rtyle/artlight/project/eagle/projects/ray/ray0.png

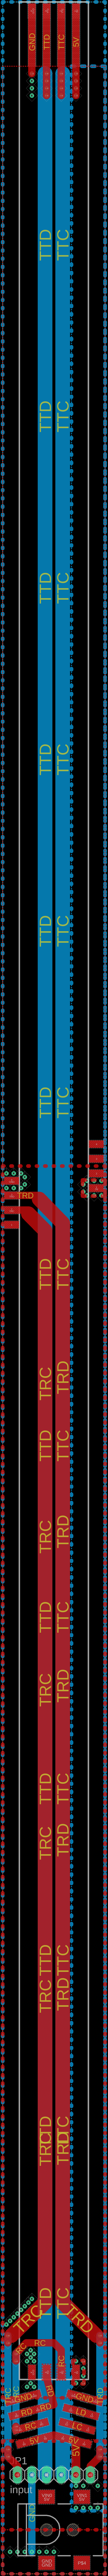
project/eagle/projects/ray/ray0.png
