rtyle/artlight/project/main/HT7M2xxxMotionSensor.cpp

#include <cinttypes>

#include "esp_log.h"

#include "HT7M2xxxMotionSensor.h"

// symmetric encode/decode for 16 bit value
// between BYTE_ORDER of our processor
// and BIG_ENDIAN encoding of device registers
static uint16_t translate(uint16_t value) {
    return
#if BYTE_ORDER == BIG_ENDIAN
    value;
#else
    __builtin_bswap16(value);
#endif
}

// scope of everything in this anonymous namespace
// is limited to this translation unit and has internal linkage
namespace {

struct RegisterKey {
    enum : uint8_t {
	configuration0			= 0x00,
	configuration1			= 0x01,
	configuration2			= 0x02,
	triggerDuration			= 0x03,
	eepromAccess			= 0x04,
	pirRawData			= 0x05,
	opticalSensorRawData		= 0x06,
	temperatureSensorRawData	= 0x07,
	status				= 0x08,
	manufacturerId			= 0x09,
	firmwareVersion			= 0x0a,
    };
};

}

HT7M2xxxMotionSensor::HT7M2xxxMotionSensor(
    asio::io_context &	io_,
    I2C::Master const *	i2cMaster_)
:
    MotionSensor	{"HT7M2xxx", io_},
    i2cMaster		{i2cMaster_}
{
    assertId();
    timer.start();
}

// how long we should wait for commands to complete
static TickType_t constexpr wait {1};

uint16_t HT7M2xxxMotionSensor::getRegister(uint8_t key) const {
    uint16_t value;
    i2cMaster->commands(address, wait)
	.writeByte(key)
	.startRead()
	.readBytes(&value, sizeof value);
    return value;
}

void HT7M2xxxMotionSensor::setRegister(uint8_t key, uint16_t value) const {
    i2cMaster->commands(address, wait)
	.writeByte(key)
	.writeBytes(&value, sizeof value);
}

void HT7M2xxxMotionSensor::assertId() const {
    assert(0x04d9 == getManufacturerId());
}

HT7M2xxxMotionSensor::Configuration0::Configuration0(
    uint16_t encoding_)
:
    encoding	{encoding_}
{}

HT7M2xxxMotionSensor::Configuration0::Configuration0(
    signed	temperatureCelsius_,
    unsigned	pirPeriod_)
:
    temperatureCelsius	{temperatureCelsius_},
    pirPeriod		{pirPeriod_}
{}

#define setter(name) HT7M2xxxMotionSensor::Configuration0 & HT7M2xxxMotionSensor::Configuration0::name##_(decltype(name) s) {name = s; return *this;}
setter(temperatureCelsius)
setter(pirPeriod)
#undef setter

HT7M2xxxMotionSensor::Configuration0
HT7M2xxxMotionSensor::getConfiguration0() const {
    return getRegister(RegisterKey::configuration0);
}

void HT7M2xxxMotionSensor::setConfiguration0(Configuration0 value) const {
    setRegister(RegisterKey::configuration0, value.encoding);
}

HT7M2xxxMotionSensor::Configuration1::Configuration1(
    uint16_t encoding_)
:
    encoding	{encoding_}
{}

HT7M2xxxMotionSensor::Configuration1::Configuration1(
    unsigned	lowVoltageDetectThreshold_,
    bool	lowVoltageDetectEnable_,
    bool	pirDetectEnable_,
    bool	pirRetrigger_,
    bool	pirTriggeredPinEnable_,
    unsigned	pirThreshold_,
    unsigned	pirGain_)
:
#if BYTE_ORDER == BIG_ENDIAN
    lowVoltageDetectThreshold	{lowVoltageDetectThreshold_},
    lowVoltageDetectEnable	{lowVoltageDetectEnable_},
    pirDetectEnable		{pirDetectEnable_},
    pirRetrigger		{pirRetrigger_},
    pirTriggeredPinEnable	{pirTriggeredPinEnable_},
    pirThreshold		{pirThreshold_},
    pirGain			{pirGain_}
#else
    pirTriggeredPinEnable	{pirTriggeredPinEnable_},
    pirRetrigger		{pirRetrigger_},
    pirDetectEnable		{pirDetectEnable_},
    lowVoltageDetectEnable	{lowVoltageDetectEnable_},
    lowVoltageDetectThreshold	{lowVoltageDetectThreshold_},
    pirGain			{pirGain_},
    pirThreshold		{pirThreshold_}
#endif
{}

#define setter(name) HT7M2xxxMotionSensor::Configuration1 & HT7M2xxxMotionSensor::Configuration1::name##_(decltype(name) s) \
    {name = s; return *this;}
setter(pirTriggeredPinEnable)
setter(pirRetrigger)
setter(pirDetectEnable)
setter(lowVoltageDetectEnable)
setter(lowVoltageDetectThreshold)
setter(pirGain)
setter(pirThreshold)
#undef setter

HT7M2xxxMotionSensor::Configuration1
HT7M2xxxMotionSensor::getConfiguration1() const {
    return getRegister(RegisterKey::configuration1);
}

void HT7M2xxxMotionSensor::setConfiguration1(Configuration1 value) const {
    setRegister(RegisterKey::configuration1, value.encoding);
}

HT7M2xxxMotionSensor::Configuration2::Configuration2(
    uint16_t encoding_)
:
    encoding	{encoding_}
{}

HT7M2xxxMotionSensor::Configuration2::Configuration2(
    unsigned	darkThreshold_,
    bool	pirDetectIfDarkEnable_,
    unsigned	address_)
:
#if BYTE_ORDER == BIG_ENDIAN
    darkThreshold		{darkThreshold_},
    pirDetectIfDarkEnable	{pirDetectIfDarkEnable_},
    address			{address_}
#else
    pirDetectIfDarkEnable	{pirDetectIfDarkEnable_},
    darkThreshold		{darkThreshold_},
    address			{address_}
#endif
{}

#define setter(name) HT7M2xxxMotionSensor::Configuration2 & HT7M2xxxMotionSensor::Configuration2::name##_(decltype(name) s) {name = s; return *this;}
setter(pirDetectIfDarkEnable)
setter(darkThreshold)
setter(address)
#undef setter

HT7M2xxxMotionSensor::Configuration2
HT7M2xxxMotionSensor::getConfiguration2() const {
    return getRegister(RegisterKey::configuration2);
}

void HT7M2xxxMotionSensor::setConfiguration2(Configuration2 value) const {
    setRegister(RegisterKey::configuration2, value.encoding);
}

unsigned HT7M2xxxMotionSensor::getDuration() const {
    return translate(getRegister(RegisterKey::triggerDuration));
}

void HT7M2xxxMotionSensor::setDuration(unsigned value) {
    MotionSensor::setDuration(value);
    setRegister(RegisterKey::triggerDuration, translate(value));
}

unsigned HT7M2xxxMotionSensor::getPirRawData() const {
    return translate(getRegister(RegisterKey::pirRawData));
}

unsigned HT7M2xxxMotionSensor::getOpticalSensorRawData() const {
    return translate(getRegister(RegisterKey::opticalSensorRawData));
}

unsigned HT7M2xxxMotionSensor::getTemperatureSensorRawData() const {
    return translate(getRegister(RegisterKey::temperatureSensorRawData));
}

HT7M2xxxMotionSensor::Status::Status(
    uint16_t encoding_)
:
    encoding	{encoding_}
{}

HT7M2xxxMotionSensor::Status HT7M2xxxMotionSensor::getStatus() const {
    return getRegister(RegisterKey::status);
}

unsigned HT7M2xxxMotionSensor::getManufacturerId() const {
    return translate(getRegister(RegisterKey::manufacturerId));
}

unsigned HT7M2xxxMotionSensor::getFirmwareVersion() const {
    return translate(getRegister(RegisterKey::firmwareVersion));
}

unsigned HT7M2xxxMotionSensor::getPeriod() const {
    return 50;	// * 10ms (tick) units
}

bool HT7M2xxxMotionSensor::readMotion() const {
#if 0
    {
	Configuration0 const c0 {getConfiguration0()};
	Configuration1 const c1 {getConfiguration1()};
	Configuration2 const c2 {getConfiguration2()};
	unsigned const duration {getDuration()};
	unsigned const pirRawData {getPirRawData()};
	ESP_LOGI(name, "\ttemperature %d°C\tpirPeriod %ums\tlowVoltageDetectThreshold %u\tlowVoltageDetectEnable %u\tpirDetectEnable %u\tpirRetrigger %u\tpirTriggeredPinEnable %u\tpirThreshold %.1fv\tpirGain %u\tdarkThreshold %u\tpirDetectIfDarkEnable %u\taddress %02x\tduration %ums\tpirRawData %u",
	    c0.temperatureCelsius,
	    pirPeriodDecode(c0.pirPeriod),
	    c1.lowVoltageDetectThreshold,
	    c1.lowVoltageDetectEnable,
	    c1.pirDetectEnable,
	    c1.pirRetrigger,
	    c1.pirTriggeredPinEnable,
	    pirThresholdDecode(c1.pirThreshold),
	    pirGainDecode(c1.pirGain),
	    c2.darkThreshold,
	    c2.pirDetectIfDarkEnable,
	    c2.address,
	    duration * 100,
	    pirRawData);
    }
#endif
#if 0
    for (auto i = 0u; ; ++i) {
	try {
	    getStatus();
	} catch (...) {
	    ESP_LOGE(name, "%p getStatus count %u", nullptr, i);
	    return false;
	}
    }
#endif
#if 0
    {
	Status const status {getStatus()};
	ESP_LOGI(name, "notReady %u\tlowVoltageDetected %u\tdark %u\tpirNoiseDetected %u\tpirRetriggered %u\tpirTriggered %u",
	    status.notReady,
	    status.lowVoltageDetected,
	    status.dark,
	    status.pirNoiseDetected,
	    status.pirRetriggered,
	    status.pirTriggered);
    }
#endif
    return getStatus().pirTriggered;
}

HT7M2xxxMotionSensor::~HT7M2xxxMotionSensor() {}
