rtyle/artlight/project/main/LuxSensor.cpp

#include "esp_log.h"

#include "LuxSensor.h"

LuxSensor::LuxSensor(char const * name_, asio::io_context & io_)
:
    name	{name_},
    io		{io_},
    lux		{0.0f},
    // asio timers are not supported
    // adapt a FreeRTOS timer to post an update
    timer{name,
	1,
	false,
	[this]() {
	    io.post([this]() {
		this->update();
	    });
	}
    }
{}

LuxSensor::~LuxSensor() {}

static TickType_t soonAfterAvailable(unsigned available) {
    return 2 + available / portTICK_PERIOD_MS;
}

void LuxSensor::update() {
    // we try to skate on the edge (just under an overflow_error)
    bool up {true};
    try {
	lux = readLux();
    } catch (std::underflow_error & e) {
#if 0
	ESP_LOGE(name, "underflow %s", e.what());
#endif
    } catch (std::overflow_error & e) {
#if 0
	ESP_LOGE(name, "overflow %s", e.what());
#endif
	up = false;
    } catch (esp_err_t & e) {
	ESP_LOGE(name, "readLux %s (0x%x)", esp_err_to_name(e), e);
    } catch (...) {
	ESP_LOGE(name, "readLux unknown error");
    }
    try {
	timer.setPeriod(soonAfterAvailable(up
	    ? increaseSensitivity()
	    : decreaseSensitivity()));
    } catch (esp_err_t & e) {
	ESP_LOGE(name, "set sensitivity %s (0x%x)", esp_err_to_name(e), e);
    } catch (...) {
	ESP_LOGE(name, "unknown error");
    }
    timer.start();
}

float LuxSensor::getLux() {return lux;}
