rtyle/artlight/project/main/GoldenArtTask.cpp

#include <array>
#include <cassert>
#include <cmath>
#include <limits>
#include <random>
#include <set>
#include <sstream>
#include <vector>

#include "esp_log.h"
extern "C" {
#include "esp_time_impl.h"
}

#include "fromString.h"
#include "Array.h"
#include "Blend.h"
#include "Contrast.h"
#include "GoldenArtTask.h"
#include "Curve.h"
#include "PerlinNoise.hpp"
#include "Timer.h"
#include "TSL2591LuxSensor.h"

constexpr float pi	{std::acos(-1.0f)};
constexpr float tau	{2.0f * pi};

// https://en.wikipedia.org/wiki/Fibonacci_number
// 0, 1, 2, 3, 4, 5, 6,  7,  8,  9, 10, 11,  12, ...
// 0, 1, 1, 2, 3, 5, 8, 13, 21, 34, 55, 89, 144, ...
static constexpr unsigned fibonacci_(unsigned a, unsigned b, unsigned i) {
    return i ? fibonacci_(b, a + b, i - 1) : a + b;
}
constexpr unsigned n0 {0};
constexpr unsigned n1 {1};
static constexpr unsigned fibonacci(unsigned i) {
    return i > 1 ? fibonacci_(n0, n1, i - 2) : i ? n1 : n0;
}

constexpr unsigned millisecondsPerSecond	{1000u};
constexpr unsigned microsecondsPerSecond	{1000000u};

#define rimEnd 1024
constexpr size_t ledCount {rimEnd};

char const * const GoldenArtTask::Mode::string[]
    {"clock", "swirl", "solid"};
GoldenArtTask::Mode::Mode(Value value_) : value(value_) {}
GoldenArtTask::Mode::Mode(char const * value) : value(
    [value](){
	size_t i {0};
	for (auto e: string) {
	    if (0 == std::strcmp(e, value)) return static_cast<Value>(i);
	    ++i;
	}
	return clock;
    }()
) {}
char const * GoldenArtTask::Mode::toString() const {
    return string[value];
}

namespace {
// A Path may be used to construct a standard input iterator
// that begins at an unsigned value,
// decrements a unsigned step (default 1) as it is advanced
// until it exhausts all unsigned values on this path.
class Path {
public:
    class Iterator: public std::iterator<std::input_iterator_tag, unsigned,
	unsigned, unsigned const *, unsigned> {
    public:
	explicit Iterator(Path const * path_)
	    : path{path_}, value{path->value} {}
	explicit Iterator()
	    : path{nullptr}, value{std::numeric_limits<value_type>::max()} {}
	Iterator & operator++() {
	    if (path) {
		if (value < path->step)
		    value = std::numeric_limits<value_type>::max();
		else
		    value -= path->step;
	    }
	    return *this;
	}
	bool operator==(Iterator that) const {return value == that.value;}
	bool operator!=(Iterator that) const {return !(*this == that);}
	reference operator*() const {return value;}
    private:
	Path const * path;
	value_type value;
    };
    Path(Iterator::value_type value_, Iterator::value_type step_ = 1) : value{value_}, step{step_} {}
    Iterator begin() {return Iterator(this);}
    Iterator end() {return Iterator();}
private:
    Iterator::value_type const value;
    Iterator::value_type const step;
};
}

static constexpr float phaseIn(uint64_t time, uint64_t period) {
    return (time % period) / static_cast<float>(period);
}

static float fade_(float high, float dim, float min, float from) {
    if (1.0f <= from || 0.0f == dim || min > high) {
	return high;		// snap high
    } else {
	if (0.0f == from && 1.0 == dim) {
	    return 0.0f;	// snap off
	} else {
	    auto const low {std::max(min, high * (1.0f - dim))};
	    return low + (high - low) * from;
	}
    }
}

void GoldenArtTask::update_() {
    // LED i [0, ledCount) is rendered like a seed in a sunflower head
    // at polar coordinate
    //	(scale * sqrt(1 + i), i * tau / phi)
    // where scale was chosen to space the LEDs adequately
    // (18 mil for SK9822 5050 (5.0 x 5.0 mm) LEDs).
    //
    // such rendering creates a family of spirals for each fibonacci number N
    // where
    // * N is the number of spirals in the family and
    // * N separates neighboring LEDs in any spiral.

    // for rendering a family of spirals,
    // it is convenient to have the outermost rim of indeces (from the end)
    // of each ordered in a clockwise manner from the top.
    // these were imported from exploratory rendering code.
    // see easyeda/projects/golden/golden.html.

    #define rimName_(end, index) rim##end##_##index
    #define rimName(end, index) rimName_(end, index)
    #define rimDecl(end, index) rimName_(end, index)[fibonacci(index)]

    struct Rim {
	unsigned const	end;
	unsigned const	fibonacciIndex;
	uint8_t const *	sequence;
    };
    #define RimArgs(end, index) {end, index, rimName(end, index)}

    static constexpr uint8_t rimDecl(rimEnd, 7) {
	0,  5, 10,  2,  7, 12,  4,  9,  1,  6, 11,  3,  8,
    };
    static constexpr uint8_t rimDecl(917, 7) {
	 3,  8,  0,  5, 10,  2,  7, 12,  4,  9,  1,  6, 11,
    };
    static constexpr uint8_t rimDecl(569, 7) {
	11,  3,  8,  0,  5, 10,  2,  7, 12,  4,  9,  1,  6,
    };
    static constexpr uint8_t rimDecl(355, 7) {
	 9,  1,  6, 11,  3,  8,  0,  5, 10,  2,  7, 12,  4,
    };
    static constexpr uint8_t rimDecl(233, 7) {
	 5, 10,  2,  7, 12,  4,  9,  1,  6, 11,  3,  8,  0,
    };
    static constexpr uint8_t rimDecl(145, 7) {
	 6, 11,  3,  8,  0,  5, 10,  2,  7, 12,  4,  9,  1,
    };
    static constexpr uint8_t rimDecl( 91, 7) {
	12,  4,  9,  1,  6, 11,  3,  8,  0,  5, 10,  2,  7,
    };
    static constexpr uint8_t rimDecl( 57, 7) {
	 7, 12,  4,  9,  1,  6, 11,  3,  8,  0,  5, 10,  2,
    };
    static constexpr Rim const rim7[] {
	RimArgs(rimEnd, 7),
	RimArgs(917, 7),
	RimArgs(569, 7),
	RimArgs(355, 7),
	RimArgs(233, 7),
	RimArgs(145, 7),
	RimArgs( 91, 7),
	RimArgs( 57, 7),
    };

    static constexpr uint8_t rimDecl(rimEnd, 8) {
	 0, 13,  5, 18, 10,  2, 15,  7, 20, 12,  4, 17,  9,  1, 14,  6,
	19, 11,  3, 16,  8,
    };
    static constexpr uint8_t rimDecl(917, 8) {
	 3, 16,  8,  0, 13,  5, 18, 10,  2, 15,  7, 20, 12,  4, 17,  9,
	 1, 14,  6, 19, 11,
    };
    static constexpr uint8_t rimDecl(582, 8) {
	 3, 16,  8,  0, 13,  5, 18, 10,  2, 15,  7, 20, 12,  4, 17,  9,
	 1, 14,  6, 19, 11,
    };
    static constexpr uint8_t rimDecl(361, 8) {
	 2, 15,  7, 20, 12,  4, 17,  9,  1, 14,  6, 19, 11,  3, 16,  8,
	 0, 13,  5, 18, 10,
    };
    static constexpr uint8_t rimDecl(225, 8) {
	10,  2, 15,  7, 20, 12,  4, 17,  9,  1, 14,  6, 19, 11,  3, 16,
	 8,  0, 13,  5, 18,
    };
    static constexpr uint8_t rimDecl(141, 8) {
	15,  7, 20, 12,  4, 17,  9,  1, 14,  6, 19, 11,  3, 16,  8,  0,
	13,  5, 18, 10,  2,
    };
    static constexpr uint8_t rimDecl( 91, 8) {
	20, 12,  4, 17,  9,  1, 14,  6, 19, 11,  3, 16,  8,  0, 13,  5,
	18, 10,  2, 15,  7,
    };
    static constexpr Rim const rim8[] {
	RimArgs(rimEnd, 8),
	RimArgs(917, 8),
	RimArgs(582, 8),
	RimArgs(361, 8),
	RimArgs(225, 8),
	RimArgs(141, 8),
	RimArgs( 91, 8),
    };

    static constexpr uint8_t rimDecl(rimEnd, 9) {
	 0, 13, 26,  5, 18, 31, 10, 23,  2, 15, 28,  7, 20, 33, 12, 25,
	 4, 17, 30,  9, 22,  1, 14, 27,  6, 19, 32, 11, 24,  3, 16, 29,
	 8, 21,
    };
    static constexpr uint8_t rimDecl(917, 9) {
	 3, 16, 29,  8, 21,  0, 13, 26,  5, 18, 31, 10, 23,  2, 15, 28,
	 7, 20, 33, 12, 25,  4, 17, 30,  9, 22,  1, 14, 27,  6, 19, 32,
	11, 24,
    };
    static constexpr uint8_t rimDecl(569, 9) {
	11, 24,  3, 16, 29,  8, 21,  0, 13, 26,  5, 18, 31, 10, 23,  2,
	15, 28,  7, 20, 33, 12, 25,  4, 17, 30,  9, 22,  1, 14, 27,  6,
	19, 32,
    };
    static constexpr uint8_t rimDecl(355, 9) {
	30,  9, 22,  1, 14, 27,  6, 19, 32, 11, 24,  3, 16, 29,  8, 21,
	 0, 13, 26,  5, 18, 31, 10, 23,  2, 15, 28,  7, 20, 33, 12, 25,
	 4, 17,
    };
    static constexpr uint8_t rimDecl(225, 9) {
	10, 23,  2, 15, 28,  7, 20, 33, 12, 25,  4, 17, 30,  9, 22,  1,
	14, 27,  6, 19, 32, 11, 24,  3, 16, 29,  8, 21,  0, 13, 26,  5,
	18, 31,
    };
    static constexpr uint8_t rimDecl(141, 9) {
	15, 28,  7, 20, 33, 12, 25,  4, 17, 30,  9, 22,  1, 14, 27,  6,
	19, 32, 11, 24,  3, 16, 29,  8, 21,  0, 13, 26,  5, 18, 31, 10,
	23, 2,
    };
    static constexpr Rim const rim9[] {
	RimArgs(rimEnd, 9),
	RimArgs(917, 9),
	RimArgs(569, 9),
	RimArgs(355, 9),
	RimArgs(225, 9),
	RimArgs(141, 9),
    };

    static constexpr uint8_t rimDecl(rimEnd, 10) {
	 0, 34, 13, 47, 26,  5, 39, 18, 52, 31, 10, 44, 23,  2, 36, 15,
	49, 28,  7, 41, 20, 54, 33, 12, 46, 25,  4, 38, 17, 51, 30,  9,
	43, 22,  1, 35, 14, 48, 27,  6, 40, 19, 53, 32, 11, 45, 24,  3,
	37, 16, 50, 29,  8, 42, 21,
    };
    static constexpr uint8_t rimDecl(907, 10) {
	27,  6, 40, 19, 53, 32, 11, 45, 24,  3, 37, 16, 50, 29,  8, 42,
	21,  0, 34, 13, 47, 26,  5, 39, 18, 52, 31, 10, 44, 23,  2, 36,
	15, 49, 28,  7, 41, 20, 54, 33, 12, 46, 25,  4, 38, 17, 51, 30,
	 9, 43, 22,  1, 35, 14, 48,
    };
    static constexpr uint8_t rimDecl(582, 10) {
	24,  3, 37, 16, 50, 29,  8, 42, 21,  0, 34, 13, 47, 26,  5, 39,
	18, 52, 31, 10, 44, 23,  2, 36, 15, 49, 28,  7, 41, 20, 54, 33,
	12, 46, 25,  4, 38, 17, 51, 30,  9, 43, 22,  1, 35, 14, 48, 27,
	 6, 40, 19, 53, 32, 11, 45,
    };
    static constexpr uint8_t rimDecl(355, 10) {
	30,  9, 43, 22,  1, 35, 14, 48, 27,  6, 40, 19, 53, 32, 11, 45,
	24,  3, 37, 16, 50, 29,  8, 42, 21,  0, 34, 13, 47, 26,  5, 39,
	18, 52, 31, 10, 44, 23,  2, 36, 15, 49, 28,  7, 41, 20, 54, 33,
	12, 46, 25,  4, 38, 17, 51,
    };
    static constexpr uint8_t rimDecl(225, 10) {
	44, 23,  2, 36, 15, 49, 28,  7, 41, 20, 54, 33, 12, 46, 25,  4,
	38, 17, 51, 30,  9, 43, 22,  1, 35, 14, 48, 27,  6, 40, 19, 53,
	32, 11, 45, 24,  3, 37, 16, 50, 29,  8, 42, 21,  0, 34, 13, 47,
	26,  5, 39, 18, 52, 31, 10,
    };
    static constexpr Rim const rim10[] {
	RimArgs(rimEnd, 10),
	RimArgs(907, 10),
	RimArgs(582, 10),
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
	42, 76, 21, 55,  0, 34, 68, 13, 47, 81, 26, 60,  5, 39, 73, 18,
	52, 86, 31, 65, 10, 44, 78, 23, 57,
    };
    static constexpr Rim const rim11[] {
	RimArgs(rimEnd, 11),
	RimArgs(907, 11),
	RimArgs(569, 11),
	RimArgs(361, 11),
    };

    static constexpr uint8_t rimDecl(rimEnd, 12) {
	  0,  89,  34, 123,  68,  13, 102,  47, 136,  81,  26, 115,  60,   5,  94,  39,
	128,  73,  18, 107,  52, 141,  86,  31, 120,  65,  10,  99,  44, 133,  78,  23,
	112,  57,   2,  91,  36, 125,  70,  15, 104,  49, 138,  83,  28, 117,  62,   7,
	 96,  41, 130,  75,  20, 109,  54, 143,  88,  33, 122,  67,  12, 101,  46, 135,
	 80,  25, 114,  59,   4,  93,  38, 127,  72,  17, 106,  51, 140,  85,  30, 119,
	 64,   9,  98,  43, 132,  77,  22, 111,  56,   1,  90,  35, 124,  69,  14, 103,
	 48, 137,  82,  27, 116,  61,   6,  95,  40, 129,  74,  19, 108,  53, 142,  87,
	 32, 121,  66,  11, 100,  45, 134,  79,  24, 113,  58,   3,  92,  37, 126,  71,
	 16, 105,  50, 139,  84,  29, 118,  63,   8,  97,  42, 131,  76,  21, 110,  55,
    };
    static constexpr uint8_t rimDecl(917, 12) {
	 37, 126,  71,  16, 105,  50, 139,  84,  29, 118,  63,   8,  97,  42, 131,  76,
	 21, 110,  55,   0,  89,  34, 123,  68,  13, 102,  47, 136,  81,  26, 115,  60,
	  5,  94,  39, 128,  73,  18, 107,  52, 141,  86,  31, 120,  65,  10,  99,  44,
	133,  78,  23, 112,  57,   2,  91,  36, 125,  70,  15, 104,  49, 138,  83,  28,
	117,  62,   7,  96,  41, 130,  75,  20, 109,  54, 143,  88,  33, 122,  67,  12,
	101,  46, 135,  80,  25, 114,  59,   4,  93,  38, 127,  72,  17, 106,  51, 140,
	 85,  30, 119,  64,   9,  98,  43, 132,  77,  22, 111,  56,   1,  90,  35, 124,
	 69,  14, 103,  48, 137,  82,  27, 116,  61,   6,  95,  40, 129,  74,  19, 108,
	 53, 142,  87,  32, 121,  66,  11, 100,  45, 134,  79,  24, 113,  58,   3,  92,
    };
    static constexpr uint8_t rimDecl(582, 12) {
	 79,  24, 113,  58,   3,  92,  37, 126,  71,  16, 105,  50, 139,  84,  29, 118,
	 63,   8,  97,  42, 131,  76,  21, 110,  55,   0,  89,  34, 123,  68,  13, 102,
	 47, 136,  81,  26, 115,  60,   5,  94,  39, 128,  73,  18, 107,  52, 141,  86,
	 31, 120,  65,  10,  99,  44, 133,  78,  23, 112,  57,   2,  91,  36, 125,  70,
	 15, 104,  49, 138,  83,  28, 117,  62,   7,  96,  41, 130,  75,  20, 109,  54,
	143,  88,  33, 122,  67,  12, 101,  46, 135,  80,  25, 114,  59,   4,  93,  38,
	127,  72,  17, 106,  51, 140,  85,  30, 119,  64,   9,  98,  43, 132,  77,  22,
	111,  56,   1,  90,  35, 124,  69,  14, 103,  48, 137,  82,  27, 116,  61,   6,
	 95,  40, 129,  74,  19, 108,  53, 142,  87,  32, 121,  66,  11, 100,  45, 134,
    };
    static constexpr Rim const rim12[] {
	RimArgs(rimEnd, 12),
	RimArgs(917, 12),
	RimArgs(582, 12),
    };

    static constexpr Array<Rim const> rim[] {
	rim12,
	rim11,
	rim10,
	rim9,
	rim8,
	rim7,
    };

    // construct static PerlinNoise objects
    static std::mt19937 rng;
    static PerlinNoise perlinNoise[] {rng, rng, rng, rng, rng};
    // Perlin noise repeats every 256 units.
    constexpr unsigned perlinNoisePeriod {256};
    constexpr uint64_t perlinNoisePeriodMicroseconds
	{perlinNoisePeriod * microsecondsPerSecond};
    // Perlin noise at an integral grid point is 0 (0.5 for noise0_1).
    // To avoid this, cut between them.

    uint64_t const microsecondsSinceBoot {esp_time_impl_get_time_since_boot()};

    Contrast const levelContrast {20.0f};

    APA102::Message<1> message0;
    {
	constexpr auto levelEnd {64.0f};	// [0, levelEnd)
	float const x {(microsecondsSinceBoot % perlinNoisePeriodMicroseconds)
	    / static_cast<float>(microsecondsPerSecond)};
	for (auto & e: message0.encodings) {
	    e = APA102::LED<> {
		static_cast<uint8_t>(levelEnd * std::nextafter(levelContrast(perlinNoise[0].noise0_1(x)), 0.0f)),
		static_cast<uint8_t>(levelEnd * std::nextafter(levelContrast(perlinNoise[1].noise0_1(x)), 0.0f)),
		static_cast<uint8_t>(levelEnd * std::nextafter(levelContrast(perlinNoise[2].noise0_1(x)), 0.0f))
	    };
	}
    }

    // clip lux blacks and whites for value to fade from
    float lux {luxSensor ? luxSensor->getLux() : white};
    if (black > lux) lux = 0.0f;
    float const fadeFrom {lux < white ? lux / white : 1.0f};

    float constexpr minLevel {4.0f / 256.0f}; // for close color
    float const fade {fade_(level, dim, minLevel, fadeFrom)};

    // nominally, we will try to render in the range of [0, levelEnd).
    // as there may be multiple (dialCount) additive renderings,
    // we must leave headroom for this.
    constexpr auto levelEndLog2	{10};
    auto const levelEnd	{fade * (1 << levelEndLog2)};

    // render with a 12 bit resolution using 16 bit signed integers.
    // these values can be clipped to 12 bit unsigned values later and
    // encoded into 8 bits later.
    APA102::LED<int16_t> led[ledCount];

    float const secondsSinceTwelveLocaltime {
	smoothTime.millisecondsSinceTwelveLocaltime(microsecondsSinceBoot)
	    / static_cast<float>(millisecondsPerSecond)};

    Rim const * rimSwirl {nullptr};	// otherwise, top of the hour celebration

    switch (mode.value) {
	case Mode::Value::clock: {
	    static SawtoothCurve const unit[dialCount] {	// [0, 1) in
		{0.0f, 60.0f * 60.0f * 12.0f},	// day		(12 hour)
		{0.0f, 60.0f * 60.0f},		// hour		(60 minute)
		{0.0f, 60.0f},			// minute	(60 second)
	    };

	    constexpr auto wavePeriod {2.0f};	// seconds
	    float ignore;
	    auto const wavePhase {std::modf(secondsSinceTwelveLocaltime / wavePeriod, &ignore)};

	    auto * width_	{width};
	    auto * curl_	{curl};
	    auto * length_	{length};
	    auto * color_	{color};
	    auto * unit_	{unit};
	    for (auto i = 0u; i < dialCount; ++i) {
		if (*width_) {
		    static APA102::LED<int16_t> const background {};
		    static APA102::LED<int16_t> const etch {-4096, -4096, -4096};
		    constexpr auto shift {levelEndLog2 - 8};

		    auto	const rim_	{rim[*curl_]};
		    auto	const rim__	{&rim_.data[std::min(*length_, rim_.size - 1)]};
		    auto	const rimSize	{fibonacci(rim__->fibonacciIndex)};
		    auto	const position	{(*unit_)(secondsSinceTwelveLocaltime)};
		    auto	const width__	{2.0f * *width_ / 64.0f};

		    APA102::LED<int16_t> color__
			{APA102::LED<int16_t>(*color_) * (1 << shift)};
		    APA102::LED<int16_t> const * foreground {&color__};
		    if (0 == i && 0 == static_cast<int>(position * 12 * 60) % 60) {
			rimSwirl = &rim_.data[0];
			foreground = &etch;
		    }

		    APA102::LED<int16_t> const faded
			{Blend<APA102::LED<int16_t>>(background, *foreground)(fade)};
		    Blend<APA102::LED<int16_t>>	const blend {background, faded};
		    HalfDial	const dial	{position, !(1 & rim__->fibonacciIndex)};
		    BellCurve<>	const bell	{0.0f, width__};

		    std::function<APA102::LED<int16_t>(float)> render {[](float){return APA102::LED<int16_t>();}};
		    switch (shape[i].value) {
			case Shape::Value::bell: {
			    render = [dial, bell, blend](float place) {
				float const offset {dial(place)};
				return blend(bell(offset));
			    };
			} break;
			case Shape::Value::wave: {
			    auto const waveWidth {2.0f / rimSize};
			    auto wavePosition {wavePhase * waveWidth};
			    if (1 & rimSize) {
				// for an odd rimSize, there is an ugly seam
				// where the wrap-around wave meets itself
				// because the sides will not be in phase.
				// we can hide this seam in the far half of
				// the dial by  shifting the wavePosition.
				// the shift must be an integral multiple
				// of waveWidth to preserve the wavePeriod.
				wavePosition += waveWidth * (0
				    + ((1 & rim__->fibonacciIndex) ? -1 : 1)
				    + std::floor((position - 0.5f) / waveWidth));
			    }
			    WaveDial const wave {wavePosition, waveWidth};
			    render = [dial, bell, wave, blend](float place) {
				auto const offset {dial(place)};
				return blend(bell(offset) * wave(place));
			    };
			} break;
			case Shape::Value::bloom: {
			    BumpCurve bump{0.0f, width__};
			    BloomCurve bloom{0.0f, width__,
				phaseIn(microsecondsSinceBoot,
				    microsecondsPerSecond << 1)};
			    render = [dial, bump, bloom, blend](float place) {
				float const offset {dial(place)};
				return blend(bump(offset) * bloom(offset));
			    };
			} break;
		    }

		    auto const closest	{static_cast<unsigned>(
			std::floor(position * rimSize + 0.5f)
		    ) % rimSize};
		    auto const * kp {rim__->sequence};
		    for (auto j {0u}; j < rimSize; ++j) {
			auto const k {*kp++};
			APA102::LED<int16_t> value {j == closest ? faded
			    : render(static_cast<float>(j) / rimSize)};
			for (auto const & l: Path{rim__->end - 1u - k, rimSize}) {
			    led[l] = led[l] + value;
			}
		    }
		}

		if (rimSwirl) break;

		++width_;
		++curl_;
		++length_;
		++color_;
		++unit_;
	    }
	} if (!rimSwirl) break;	// else, fall through
	// no break
	case Mode::Value::swirl: {
	    // ramp up and down by even offsets
	    // so that there are fewer changes in direction
	    static constexpr Rim rimCycle[] {
		RimArgs(rimEnd,  7),
		RimArgs(rimEnd,  9),
		RimArgs(rimEnd, 11),
		RimArgs(rimEnd, 12),
		RimArgs(rimEnd, 10),
		RimArgs(rimEnd,  8),
	    };
	    static constexpr auto rimCycleSize	{sizeof(rimCycle) / sizeof(*rimCycle)};

	    constexpr auto radiusMax	{1.5f};
	    constexpr auto iSeconds	{60u};	// covers one swirl in cycle
	    constexpr auto zSeconds	{8u};	// covers perlin noise period

	    float const z {((microsecondsSinceBoot / zSeconds) % perlinNoisePeriodMicroseconds)
		/ static_cast<float>(microsecondsPerSecond)};

	    Contrast const radiusContrast {10.0f};
	    float const r {radiusMax * radiusContrast(perlinNoise[3].noise0_1(z))};

	    auto const rim {rimSwirl ? rimSwirl : &rimCycle[static_cast<unsigned>(
		((microsecondsSinceBoot / iSeconds) % (rimCycleSize * microsecondsPerSecond))
		    / static_cast<float>(microsecondsPerSecond)
	    )]};
	    auto const n {fibonacci(rim->fibonacciIndex)};

	    auto kp {rim->sequence};
	    for (auto j = 0; j < n; ++j) {
		auto k {*kp++};
		float const a {tau * j / n};
		float const x {r * std::cos(a)};
		float const y {r * std::sin(a)};
		APA102::LED<int16_t> value {
		    static_cast<int16_t>(levelEnd * std::nextafter(levelContrast(perlinNoise[0].noise0_1(x, y, z)), 0.0f)),
		    static_cast<int16_t>(levelEnd * std::nextafter(levelContrast(perlinNoise[1].noise0_1(x, y, z)), 0.0f)),
		    static_cast<int16_t>(levelEnd * std::nextafter(levelContrast(perlinNoise[2].noise0_1(x, y, z)), 0.0f))
		};
		for (auto const & l: Path{rim->end - 1u - k, n}) {
		    led[l] = rimSwirl ? led[l] + value : value;
		}
	    }
	} break;
	default: {
	    float const x {(microsecondsSinceBoot % perlinNoisePeriodMicroseconds)
		/ static_cast<float>(microsecondsPerSecond)};
	    APA102::LED<int16_t> value {
		static_cast<int16_t>(levelEnd * std::nextafter(levelContrast(perlinNoise[0].noise0_1(x)), 0.0f)),
		static_cast<int16_t>(levelEnd * std::nextafter(levelContrast(perlinNoise[1].noise0_1(x)), 0.0f)),
		static_cast<int16_t>(levelEnd * std::nextafter(levelContrast(perlinNoise[2].noise0_1(x)), 0.0f))
	    };
	    for (auto & e: led) {
		e = value;
	    }
	} break;
    }

    // the natural rendering indeces need to be mapped to the path indeces
    // that reflect the way the LEDs are actually wired (addressed).
    // this order is conducive for board/trace layout.
    // see easyeda/projects/golden/scripts/goldenPath.js
    static constexpr uint16_t layout[ledCount] {
	   0,    4,    8,    2,    6,    9,    3,    7,    1,    5,   22,   13,   18,   10,   15,   20,
	  12,   17,   23,   14,   19,   11,   16,   21,   29,   38,   24,   33,   42,   27,   36,   45,
	  31,   40,   25,   34,   43,   28,   37,   47,   32,   41,   26,   35,   44,   30,   39,   49,
	  61,   73,   54,   66,   46,   58,   70,   51,   63,   75,   56,   68,   48,   60,   72,   53,
	  65,   77,   57,   69,   50,   62,   74,   55,   67,   79,   59,   71,   52,   64,   76,   89,
	 102,   81,   94,  107,   86,   99,   78,   91,  104,   83,   96,  109,   88,  101,   80,   93,
	 106,   85,   98,  111,   90,  103,   82,   95,  108,   87,  100,  114,   92,  105,   84,   97,
	 110,  130,  151,  117,  138,  159,  125,  146,  112,  133,  154,  120,  141,  162,  128,  149,
	 115,  136,  157,  123,  144,  165,  131,  152,  118,  139,  160,  126,  147,  113,  134,  155,
	 121,  142,  163,  129,  150,  116,  137,  158,  124,  145,  166,  132,  153,  119,  140,  161,
	 127,  148,  169,  135,  156,  122,  143,  164,  185,  206,  172,  193,  214,  180,  201,  167,
	 188,  209,  175,  196,  217,  183,  204,  170,  191,  212,  178,  199,  220,  186,  207,  173,
	 194,  215,  181,  202,  168,  189,  210,  176,  197,  218,  184,  205,  171,  192,  213,  179,
	 200,  221,  187,  208,  174,  195,  216,  182,  203,  224,  190,  211,  177,  198,  219,  240,
	 261,  227,  248,  269,  235,  256,  222,  243,  264,  230,  251,  272,  238,  259,  225,  246,
	 267,  233,  254,  275,  241,  262,  228,  249,  270,  236,  257,  223,  244,  265,  231,  252,
	 273,  239,  260,  226,  247,  268,  234,  255,  276,  242,  263,  229,  250,  271,  237,  258,
	 279,  245,  266,  232,  253,  274,  296,  317,  283,  304,  325,  291,  312,  277,  299,  320,
	 286,  307,  328,  294,  315,  281,  302,  323,  289,  310,  331,  297,  318,  284,  305,  326,
	 292,  313,  278,  300,  321,  287,  308,  329,  295,  316,  282,  303,  324,  290,  311,  333,
	 298,  319,  285,  306,  327,  293,  314,  280,  301,  322,  288,  309,  330,  353,  374,  340,
	 361,  382,  348,  369,  335,  356,  377,  343,  364,  385,  351,  372,  338,  359,  380,  346,
	 367,  332,  354,  375,  341,  362,  383,  349,  370,  336,  357,  378,  344,  365,  387,  352,
	 373,  339,  360,  381,  347,  368,  334,  355,  376,  342,  363,  384,  350,  371,  337,  358,
	 379,  345,  366,  389,  415,  441,  399,  425,  451,  409,  435,  393,  419,  445,  403,  429,
	 386,  413,  439,  397,  423,  449,  407,  433,  391,  417,  443,  401,  427,  453,  411,  437,
	 395,  421,  447,  405,  431,  388,  414,  440,  398,  424,  450,  408,  434,  392,  418,  444,
	 402,  428,  454,  412,  438,  396,  422,  448,  406,  432,  390,  416,  442,  400,  426,  452,
	 410,  436,  394,  420,  446,  404,  430,  456,  482,  508,  466,  492,  518,  476,  502,  460,
	 486,  512,  470,  496,  522,  480,  506,  464,  490,  516,  474,  500,  458,  484,  510,  468,
	 494,  520,  478,  504,  462,  488,  514,  472,  498,  455,  481,  507,  465,  491,  517,  475,
	 501,  459,  485,  511,  469,  495,  521,  479,  505,  463,  489,  515,  473,  499,  457,  483,
	 509,  467,  493,  519,  477,  503,  461,  487,  513,  471,  497,  523,  557,  591,  536,  570,
	 604,  549,  583,  528,  562,  596,  541,  575,  609,  554,  588,  533,  567,  601,  546,  580,
	 525,  559,  593,  538,  572,  606,  551,  585,  530,  564,  598,  543,  577,  611,  556,  590,
	 535,  569,  603,  548,  582,  527,  561,  595,  540,  574,  608,  553,  587,  532,  566,  600,
	 545,  579,  524,  558,  592,  537,  571,  605,  550,  584,  529,  563,  597,  542,  576,  610,
	 555,  589,  534,  568,  602,  547,  581,  526,  560,  594,  539,  573,  607,  552,  586,  531,
	 565,  599,  544,  578,  612,  646,  680,  625,  659,  693,  638,  672,  617,  651,  685,  630,
	 664,  698,  643,  677,  622,  656,  690,  635,  669,  614,  648,  682,  627,  661,  695,  640,
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
    };

    // transfer APA102::LED<int16_t> renderings to message layout
    // with gamma correction and scaled encodings.
    APA102::Message<ledCount> message1;
    auto i = 0u;
    for (auto & e: led) {
	int16_t ps[3] {
	    e.part.red,
	    e.part.green,
	    e.part.blue,
	};
	for (auto & p: ps) {
	    if (p) {
		constexpr int16_t max {0xfff};
		auto out {static_cast<int16_t>(
		    0.5f + max * std::pow(static_cast<float>(p) / max, gamma))};
		if (!out) out = 1;
		p = out;
	    }
	}
	message1.encodings[layout[i++]]
	    = APA102::LED<int16_t>(ps[0], ps[1], ps[2]);
    }

    // SPI::Transaction constructor queues the message.
    // SPI::Transaction destructor waits for result.
    {
	SPI::Transaction transaction0(spiDevice[0], SPI::Transaction::Config()
	    .tx_buffer_(&message0)
	    .length_(message0.length()));
	SPI::Transaction transaction1(spiDevice[1], SPI::Transaction::Config()
	    .tx_buffer_(&message1)
	    .length_(message1.length()));
    }
}

void GoldenArtTask::update() {
    // if the rate at which we complete work
    // is less than the periodic demand for such work
    // the work queue will eventually exhaust all memory.
    if (updated++) {
	// catch up to the rate of demand
	ESP_LOGW(name, "update rate too fast. %u", updated - 1);
	return;
    }
    update_();
    // ignore any queued update work
    io.poll();
    updated = 0;
}

static constexpr char const * const curlKey[DialPreferences::dialCount] {
    "aCurl",
    "bCurl",
    "cCurl",
};
static constexpr char const * const lengthKey[DialPreferences::dialCount] {
    "aLength",
    "bLength",
    "cLength",
};

void GoldenArtTask::curlObserved(size_t index, char const * value_) {
    unsigned value = fromString<unsigned>(value_);
    if (value < 6) {
	io.post([this, index, value](){
	    curl[index] = value;
	});
    }
}
void GoldenArtTask::lengthObserved(size_t index, char const * value_) {
    unsigned value = fromString<unsigned>(value_);
    if (value < 8) {
	io.post([this, index, value](){
	    length[index] = value;
	});
    }
}

GoldenArtTask::GoldenArtTask(
    KeyValueBroker &	keyValueBroker)
:
    AsioTask		{"GoldenArtTask", 5, 0x10000, 1},
    TimePreferences	{io, keyValueBroker, 512},
    DialPreferences	{io, keyValueBroker},

    tinyPicoLedPower {GPIO_NUM_13, GPIO_MODE_OUTPUT},

    spiBus {
	{HSPI_HOST, SPI::Bus::Config()	// tinyPico on-oboard LED
	    .mosi_io_num_(2)
	    .sclk_io_num_(12),
	0},
	{VSPI_HOST, SPI::Bus::Config()
	    .mosi_io_num_(SPI::Bus::VspiConfig.mosi_io_num)
	    .sclk_io_num_(SPI::Bus::VspiConfig.sclk_io_num)
	    .max_transfer_sz_(APA102::messageBits(ledCount)),
	1},
    },

    spiDevice {
	{&spiBus[0], SPI::Device::Config()
	    .mode_(APA102::spiMode)
	    .clock_speed_hz_( 100000)	// see SPI_MASTER_FREQ_*
	    .spics_io_num_(-1)		// no chip select
	    .queue_size_(1)
	},
	{&spiBus[1], SPI::Device::Config()
	    .mode_(APA102::spiMode)
	    .clock_speed_hz_(8000000)	// see SPI_MASTER_FREQ_*
	    .spics_io_num_(-1)		// no chip select
	    .queue_size_(1)
	},
    },

    // internal pullups on silicon are rather high (~50k?)
    // external 4.7k is still too high. external 1k works
    i2cMaster {
	I2C::Config()
	    .sda_io_num_(GPIO_NUM_21) //.sda_pullup_en_(GPIO_PULLUP_ENABLE)
	    .scl_io_num_(GPIO_NUM_22) //.scl_pullup_en_(GPIO_PULLUP_ENABLE)
	    .master_clk_speed_(400000),	// I2C fast mode
	I2C_NUM_0, 0
    },

    sensorTask	{},
    luxSensor	{[this]() -> LuxSensor * {
	    try {
		return new TSL2591LuxSensor(sensorTask.io, &i2cMaster);
	    } catch (esp_err_t & e) {
		ESP_LOGE(name, "TSL2591 %s (0x%x): disabled", esp_err_to_name(e), e);
		return nullptr;
	    } catch (...) {
		ESP_LOGE(name, "TSL2591 unknown error: disabled");
		return nullptr;
	    }
	}()
    },

    mode	{Mode::clock},
    curl	{4, 2, 0,},
    length	{2, 1, 0,},
    black	{1.0f / (1 << 10)},
    white	{1.0f * (1 <<  4)},
    level	{},
    dim		{},
    gamma	{10 / 10.f},

    modeObserver{keyValueBroker, "mode", mode.toString(),
	[this](char const * value){
	    Mode mode_(value);
	    io.post([this, mode_](){
		mode = mode_;
	    });
	}},
    curlObserver {
	{keyValueBroker, curlKey[0], "4",
	    [this](char const * value) {curlObserved(0, value);}},
	{keyValueBroker, curlKey[1], "2",
	    [this](char const * value) {curlObserved(1, value);}},
	{keyValueBroker, curlKey[2], "0",
	    [this](char const * value) {curlObserved(2, value);}},
    },
    lengthObserver {
	{keyValueBroker, lengthKey[0], "2",
	    [this](char const * value) {lengthObserved(0, value);}},
	{keyValueBroker, lengthKey[1], "1",
	    [this](char const * value) {lengthObserved(1, value);}},
	{keyValueBroker, lengthKey[2], "0",
	    [this](char const * value) {lengthObserved(2, value);}},
    },
    blackObserver {keyValueBroker, "black", "10",
	[this](char const * value_) {
	    unsigned const value {fromString<unsigned>(value_)};
	    io.post([this, value](){
		black = 1.0f / (1 << value);
	    });
	}
    },
    whiteObserver {keyValueBroker, "white", "4",
	[this](char const * value_) {
	    unsigned const value {fromString<unsigned>(value_)};
	    io.post([this, value](){
		white = 1.0f * (1 << value);
	    });
	}
    },
    levelObserver{keyValueBroker, "level", "2048",
	[this](char const * value_){
	    float value {std::min(1.0f, (0.5f + fromString<unsigned>(value_)) / 4096.0f)};
	    if (0.0f <= value && value <= 1.0f) {
		io.post([this, value](){
		    level = value;
		});
	    }
	}},
    dimObserver{keyValueBroker, "dim", "4032",
	[this](char const * value_){
	    float value {std::min(1.0f, (0.5f + fromString<unsigned>(value_)) / 4096.0f)};
	    if (0.0f <= value && value <= 1.0f) {
		io.post([this, value](){
		    dim = value;
		});
	    }
	}},
    gammaObserver{keyValueBroker, "gamma", "10",
	[this](char const * value){
	    unsigned const gamma_ = std::strtoul(value, nullptr, 10);
	    if (5 <= gamma_ && gamma_ <= 30) {
		io.post([this, gamma_](){
		    gamma = gamma_ / 10.0f;
		});
	    }
	}},

    updated {0}
{
    tinyPicoLedPower.set_level(0);	// high side switch, low (0) turns it on
}

void GoldenArtTask::run() {
    sensorTask.start();

    // asio timers are not supported
    // adapt a FreeRTOS timer to post timeout to this task.
    Timer updateTimer(name, 4, true, [this](){
	io.post([this](){
	    this->update();
	});
    });

    updateTimer.start();

    // create some dummy work ...
    asio::io_service::work work(io);

    // ... so that we will run forever
    AsioTask::run();
}

GoldenArtTask::~GoldenArtTask() {
    stop();
    ESP_LOGI(name, "~GoldenArtTask");
}
