rtyle/artlight/project/main/DialPreferences.h

#pragma once

#include "asio.hpp"

#include "APA102.h"
#include "KeyValueBroker.h"

/// A DialPreferences is a base class for an implementation that
/// that supports preferences for LED dial indicators

class DialPreferences {
private:
    asio::io_context & io_;

public:
    static constexpr size_t dialCount {3};

    struct Shape {
    private:
	static char const * const string[];
    public:
	enum Value {bell, wave, bloom} value;
	Shape(Value);
	Shape(char const *);
	char const * toString() const;
    };

    void widthObserved(size_t index, char const * value);
    void colorObserved(size_t index, char const * value);
    void shapeObserved(size_t index, char const * value);

protected:
    float				width[dialCount];
    APA102::LED<>			color[dialCount];
    Shape				shape[dialCount];

    KeyValueBroker::Observer const	widthObserver[dialCount];
    KeyValueBroker::Observer const	colorObserver[dialCount];
    KeyValueBroker::Observer const	shapeObserver[dialCount];

    DialPreferences(
	asio::io_context &	io,
	KeyValueBroker &	keyValueBroker);
};
