rtyle/artlight/project/main/Array.h

#pragma once

/// Like std::array, Array describes an array by its size and data.
/// Unlike std::array, an array of ragged Array objects can be created
/// because there can be a common_type (the types don't depend on their sizes).
/// Given an array, the constructor can deduce its size and point to the data.
template <typename T>
struct Array {
    std::size_t const size;
    T * const data;

    template <std::size_t size_>
    constexpr Array(T (&data_)[size_]) : size{size_}, data{data_} {}

    T & operator[](std::size_t i) const {return data[i];}
};
