rtyle/artlight/project/main/Preferences.h

#pragma once

#include "Httpd.h"
#include "KeyValueBroker.h"
#include "MDNS.h"

// A Preferences object starts an HTTP server that serves
//	* html at its root
//	* keyValueBroker.serialize at data
//	* keyValueBroker.serializeDefault at dataDefault
//
// A Preferences object will publish the fields (through its keyValueBroker)
// of the query string in the URL generated on a form submit by the html.
// It is important that the name attribute values used for form input elements
// correspond to the keys used in the keyValueBroker.
//
// AJAX scripts from the html can be used to populate the input elements
// of a form from the Preference object's keyValueBroker data.
// For example, the following jQuery script will use AJAX to get the JSON data
// (an object of key/name/id, value pairs), locate each identified DOM element
// and set the value of its "value" attribute.
// It is important that the id attribute values used for elements
// correspond to the keys used in the keyValueBroker.
//
//	<script src="http://code.jquery.com/jquery-3.3.1.js"></script>
//	<script>
//		$(document).ready(function(){
//			$.ajax({
//				url: 		'data',
//				type:		'GET',
//				dataType:	'json',
//				cache:		false,
//			})
//				.done(function(idValues) {
//					for (const [id, value] of Object.entries(idValues)) {
//						$('#' + id).attr('value', value);
//					}
//				})
//				.fail(function(xhr, status, error){
//					alert('Unable to load values into form');
//					console.log('error: '  + error);
//					console.log('status: ' + status);
//					console.dir(xhr);
//				})
//	});
//	</script>

class Preferences : public Httpd {
private:
    char const *	html;
    KeyValueBroker &	keyValueBroker;
    char const * const	favicon;
    size_t const	faviconSize;
    MDNS::Service	mdnsService;
    Httpd::Uri const	uri[2];
    Httpd::Uri const	uriPost[2];
    Httpd::Uri const	dataUri;
    Httpd::Uri const	dataDefaultUri;
    Httpd::Uri const	faviconUri;

    esp_err_t get(httpd_req_t * req);
    esp_err_t post(httpd_req_t * req);
public:
    Preferences(
	char const *		html,
	KeyValueBroker &	keyValueBroker,
	char const *		favicon,
	size_t			faviconSize);
};
