rtyle/artlight/project/main/Pulse.h

#pragma once

/// Pulse is a monotonically increasing function (object)
/// that, when compared to its Identity function,
/// pulses count times over a period of 1.
/// A count of 0 is the identity function.
/// The function can be made to pulseFirst at 0 or not.
class Pulse {
private:
    float const factor;
    float const sign;
public:
    Pulse(float count = 1, bool pulseFirst = false);
    float operator () (float x) const;
};
