rtyle/artlight/project/main/SmoothTime.h

#pragma once

#include <cstdint>
#include <ctime>

class SmoothTime {
private:
    char const *	name;
    size_t const	stepCount;
    size_t		stepLeft;
    float		stepProduct;
    float		stepFactor;
    int64_t		lastBootTime;
public:
    SmoothTime(char const * name, size_t count);
    int64_t	microsecondsSinceEpoch(uint64_t microsecondsSinceBoot);
    uint32_t	millisecondsSinceTwelveLocaltime(uint64_t microsecondsSinceBoot);
};
