rtyle/artlight/project/main/TimeUpdate.h

#pragma once

#include <vector>

#include "KeyValueBroker.h"

/// A TimeUpdate object configures and starts a polling SNTP client
/// that will run (in the LwIP task) for its lifetime.
/// Without notice (boo!), time will be set (jumped) using settimeofday.
/// As there is no consideration for how long it takes for the SNTP server's
/// response to reach us, it is best if the server is close (response is fast).
class TimeUpdate {
private:
    char const * const			name;
    std::vector<char *>			timeServers;
    KeyValueBroker::Observer const	timeServersObserver;

public:
    TimeUpdate(
	char const *		name,
	KeyValueBroker &	keyValueBroker);

    ~TimeUpdate();
};
